laneboysrc/nrf24l01-rc/nrf24le1-receiver/firmware/platform.h

#ifndef __PLATFORM_H__
#define __PLATFORM_H__

#include <stdint.h>
#include <nrf24le1.h>


// The preprocessour output is only available on the NRF24LE1 module hardware,
// but not on the XR3100 and HKR3000 hardware as the UART pins on those are
// used for another purpose.
// One can use the CPPM output instead on HKR3000 and XR3100
#if HARDWARE != NRF24LE1_MODULE
    #undef ENABLE_PREPROCESSOR_OUTPUT
    #undef ENABLE_UART
#else
    #ifdef ENABLE_PREPROCESSOR_OUTPUT
        #define ENABLE_UART
    #elif !defined NODEBUG
        #define ENABLE_UART
    #endif
#endif


#define __SYSTICK_IN_MS 16

// Note: the original HKR3000 is a 3-channel receiver, but our custom code
// also supports a modified version of the protocol that can handle 4 channels.
#define NUMBER_OF_CHANNELS 4
#define SERVO_PULSE_CENTER 1500
#define INITIAL_ENDPOINT_DELTA 200

#define TIMER_VALUE_US(x) (0xffff - ((uint32_t)(__SYSTEM_CLOCK / 1000) / 12 * x / 1000))


// ****************************************************************************
// IO pins: (nRF24LE1 module 15x21 mm with 32pin QFN)
//
// Note: the pin numbers in the brackets refer to the module pinout, not
// the nRF24LE1 IC pinout!
//
//            Our board             XR3100      HKR3000
//
// P0.0                             LED green
// P0.1  (4 ) LED                   LED red
// P0.2
// P0.3  (8 ) Tx                    BIND        SDA
// P0.4  (9 ) Rx                                SCL
// P0.5  (10) CH1 / FSCK            CH1         CH1
// P0.6  (12) BIND                              BIND
// P0.7  (13) CH2 / FMOSI           CH2         CH2
// P1.0  (14) CH3 / FMISO           CH3         CH3
// P1.1  (15) FCSN                  CH4         CH4
// P1.2                                         LED green
// P1.3                             SCL         LED red
// P1.4                             SDA
// P1.5
// P1.6
//
// 3.3V  (5 )
// GND   (11)
// PROG  (7 )
// RESET (19)
//
// NOTE: this firmware does not make use of the EEPROM on the HobbyKing
// receivers. Bind data is always stored in the NV memory of the nRF24LE1.
//
// ****************************************************************************


// ****************************************************************************
// IO PORT INITIALIZATION
//
// All unused ports are switched to output and 0
// When the UART Tx is used (preprocessor!), P0.3 needs to be configured as
// output and set to 1 for the Tx function to work.
// All servo outputs have to be switched to high until the first
// transmitter pulse is received to prevent the servos glitching at
// power on.
// ****************************************************************************
#if HARDWARE == XR3100
    #define GPIO_BIND P0_3
    #define GPIO_LED_GREEN P0_0
    #define GPIO_LED P0_1
    #define GPIO_CH1 P0_5
    #define GPIO_CH2 P0_7
    #define GPIO_CH3 P1_0
    #define GPIO_CH4 P1_1
    #define GPIO_PPM P1_1
    //#define GPIO_SDA P1_3
    //#define GPIO_SCL P1_4

    #define GPIO_INIT() \
    P0 = 0xa0; \
    P0DIR = 0x08;    /* P0.3 is inputs, rest outputs */ \
    P1 = 0x03; \
    P1DIR = 0x18;    /* P1.3 and P1.4 are inputs, rest outputs */ \
    P0CON = 0x53;    /* Enable pull-up on bind button P0.3 */ \
    P1CON = 0x53;    /* Enable pull-up on SDA P1.3 */ \
    P1CON = 0x54;    /* Enable pull-up on SCL P1.4 */

#elif HARDWARE == HKR3000
    #define GPIO_BIND P0_6
    #define GPIO_LED_GREEN P1_2
    #define GPIO_LED P1_3
    #define GPIO_CH1 P0_5
    #define GPIO_CH2 P0_7
    #define GPIO_CH3 P1_0
    #define GPIO_CH4 P1_1
    #define GPIO_PPM P1_1
    //#define GPIO_SDA P0_3
    //#define GPIO_SCL P0_4

    #define GPIO_INIT() \
    P0 = 0xa0; \
    P0DIR = 0x58;    /* P0.3, P0.4 and P0.6 are inputs, rest outputs */ \
    P1 = 0x03; \
    P1DIR = 0x00;    /* All P1 ports are output */ \
    P0CON = 0x53;    /* Enable pull-up on SDA P0.3 */ \
    P0CON = 0x54;    /* Enable pull-up on SCL P0.4 */ \
    P0CON = 0x56;    /* Enable pull-up on bind button P0.6 */ \

#else // HARDWARE == NRF24LE1_MODULE
    #define GPIO_BIND P0_6
    #define GPIO_LED P0_1
    #define GPIO_CH1 P0_5
    #define GPIO_CH2 P0_7
    #define GPIO_CH3 P1_0
    #define GPIO_CH4 P0_3   // Shared with Tx pin function
    #define GPIO_PPM P1_1

    #define GPIO_INIT() \
    P0 = 0xa8;       /* P0.3, P0.5, P0.7 set to 1 */ \
    P0DIR = 0x40;    /* All P0 ports except P0.6 are output */ \
    P1 = 0x03;       /* P1.0, P1.1 set to 1 */ \
    P1DIR = 0x00;    /* All P1 ports are output */ \
    P0CON = 0x56;    /* Enable pull-up on bind button P0.6 */ \

#endif


// ****************************************************************************
// Timer allocation
//
// Timer 0 provides a systick every 16ms, which is the interval in
// which servo pulses are output
//
// Timer 1 generates individual servo pulses. Its interrupt runs at highest
// priority to guarantee accurate servo pulses.
//
// Timer 2 is the hop timer.
//
// ****************************************************************************


void delay_us(uint16_t microseconds);

#endif // __PLATFORM_H__
