laneboysrc/nrf24l01-rc/nrf24le1-receiver/firmware/persistent_storage.h

#ifndef __PERSISTENT_STORAGE_H__
#define __PERSISTENT_STORAGE_H__

#define NUMBER_OF_PERSISTENT_ELEMENTS 26

void load_persistent_storage(uint8_t *data);
void save_persistent_storage(uint8_t *new_data);

#endif
