laneboysrc/nrf24l01-rc/nrf24le1-receiver/firmware/spi.c

#include <stdlib.h>
#include <stdint.h>

#include <platform.h>
#include <spi.h>



// ****************************************************************************
void init_spi(void)
{
    // Nothing to do for the nRF24LE1, which has an internal SPI via registers
}


// ****************************************************************************
uint8_t spi_transaction(uint8_t count, uint8_t __xdata *buffer)
{
    uint8_t __xdata *ptr = buffer;

    RFCON_rfcsn = 0;

    while (count--) {
        SPIRDAT = *ptr;

        // Wait for SPIF
        while (!(SPIRSTAT & 0x02));

        *ptr = SPIRDAT;
        ++ptr;
    }

    RFCON_rfcsn = 1;

    return *buffer;
}
